mamaheux/bass-amplifier/cases/footswitch/plates/side_right.SLDPRT

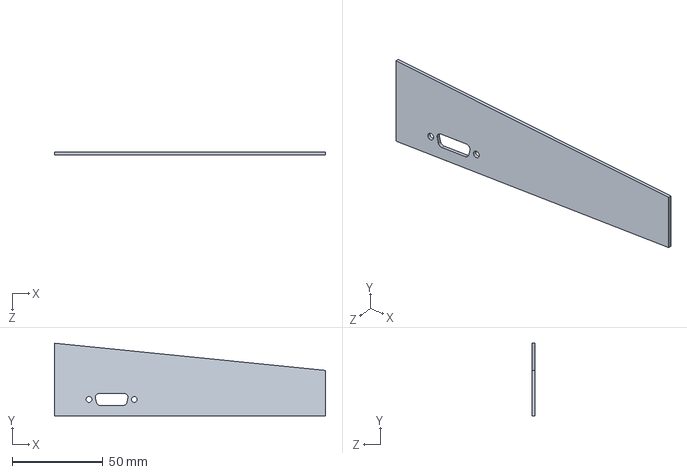
[picture p21: CAD file, 2020-08-28]
cases/footswitch/plates/side_right.SLDPRT
149.2 x 40.0 x 1.59 mm
