mamaheux/bass-amplifier/cases/amplifier/pieces/led_green.SLDPRT

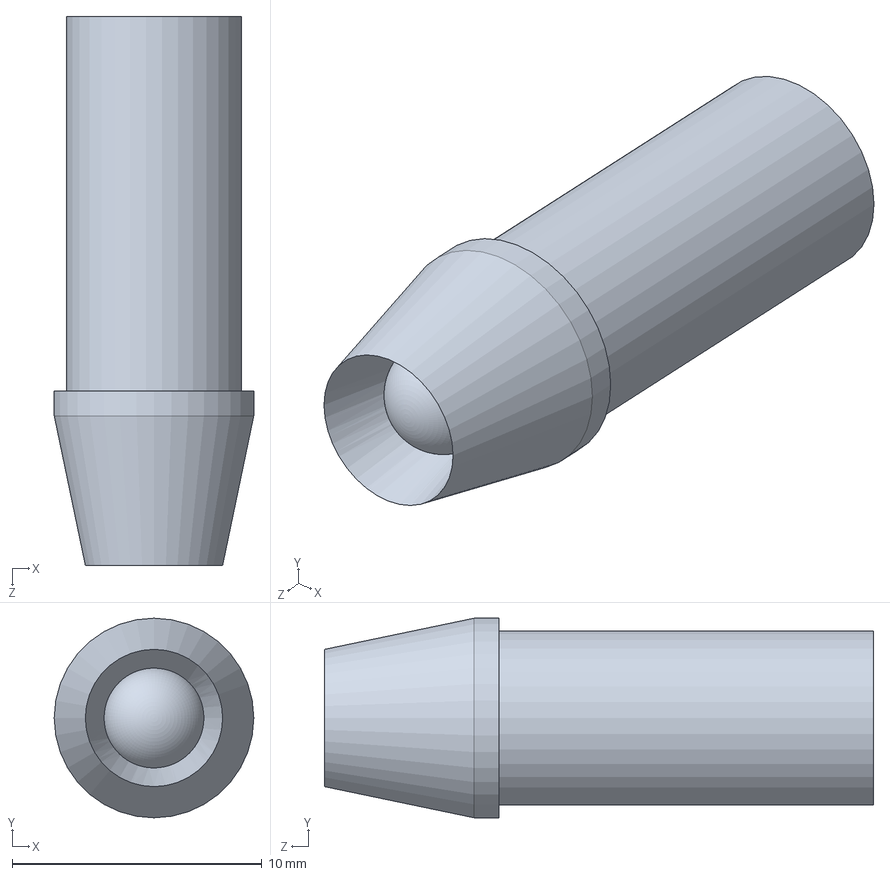
[picture p22: CAD file, 2020-08-28]
cases/amplifier/pieces/led_green.SLDPRT
8.00 x 8.00 x 22.0 mm
