mamaheux/bass-amplifier/cases/amplifier/plates/middle.SLDPRT

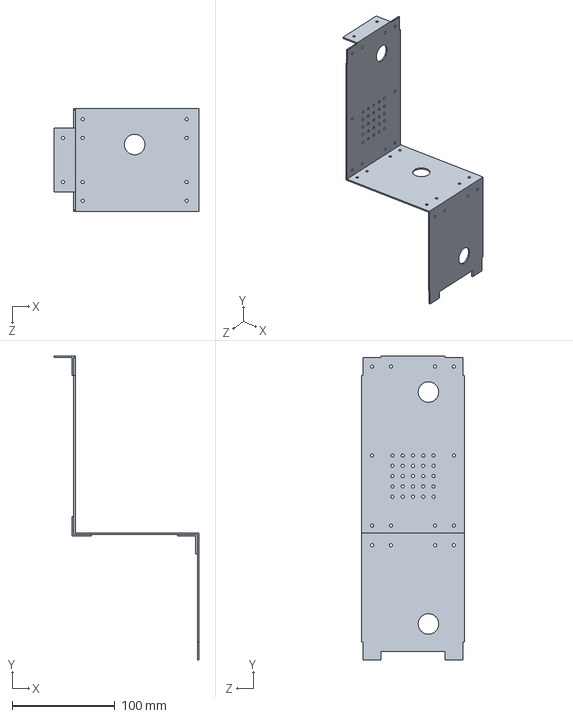
[picture p23: CAD file, 2020-08-28]
cases/amplifier/plates/middle.SLDPRT
140.6 x 295.2 x 100.0 mm
