mamaheux/bass-amplifier/cases/footswitch/pieces/led_red.SLDPRT

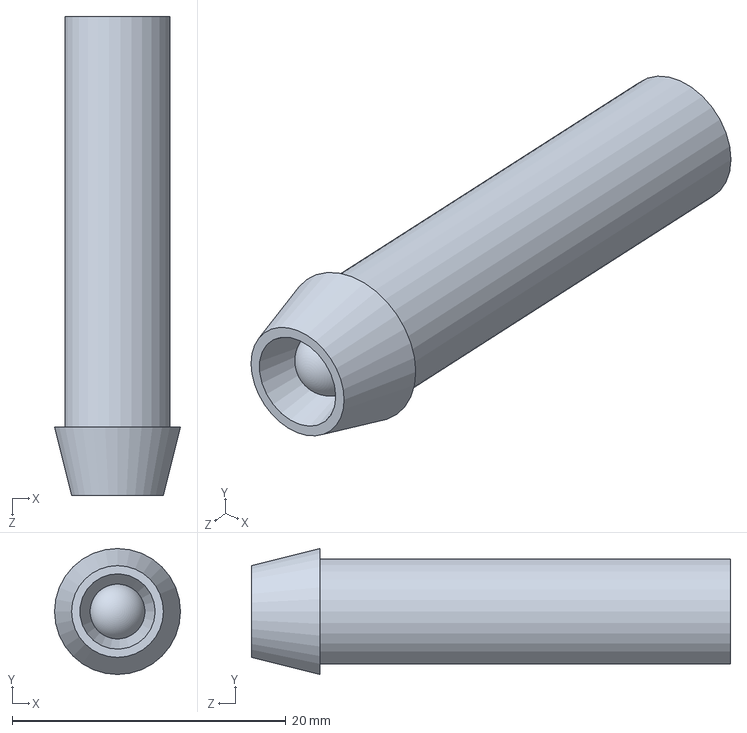
[picture p24: CAD file, 2020-08-28]
cases/footswitch/pieces/led_red.SLDPRT
9.20 x 9.20 x 35.0 mm
