mamaheux/bass-amplifier/cases/amplifier/pieces/transformer_600VA_50V.SLDPRT

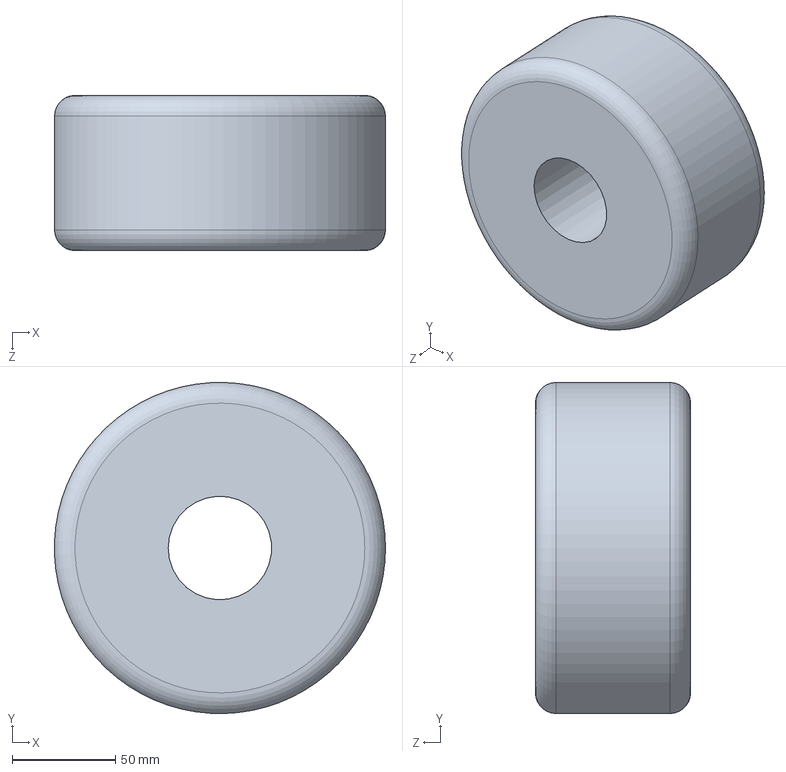
[picture p25: CAD file, 2020-08-28]
cases/amplifier/pieces/transformer_600VA_50V.SLDPRT
159.9 x 160.0 x 75.0 mm
