mamaheux/bass-amplifier/cases/footswitch/pieces/standoff_m3_10mm.SLDPRT

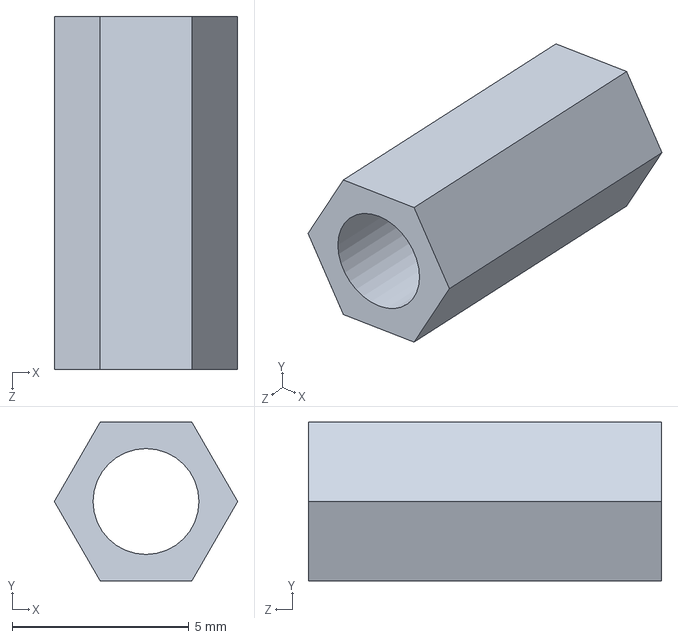
[picture p26: CAD file, 2020-08-28]
cases/footswitch/pieces/standoff_m3_10mm.SLDPRT
5.20 x 4.50 x 10.0 mm
