mamaheux/bass-amplifier/cases/amplifier/pieces/iec_c14.SLDPRT

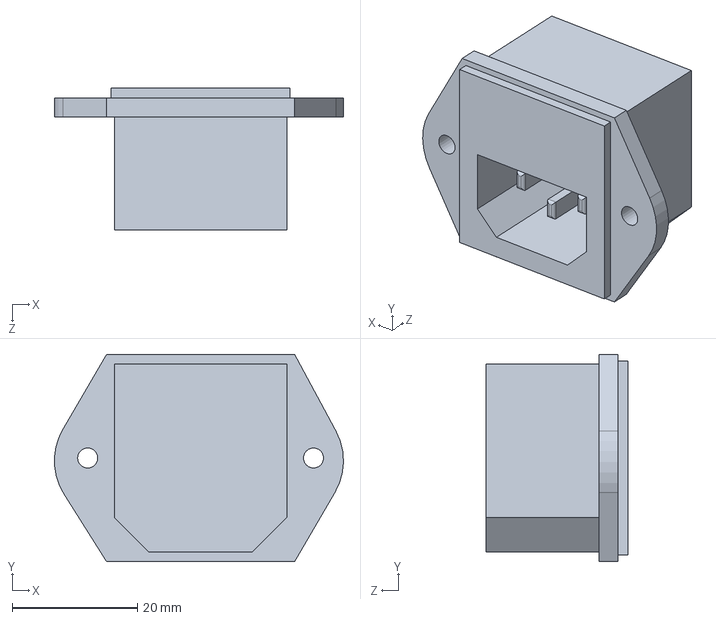
[picture p27: CAD file, 2020-08-28]
cases/amplifier/pieces/iec_c14.SLDPRT
46.1 x 33.0 x 22.6 mm
