mamaheux/bass-amplifier/cases/amplifier/plates/bottom.SLDPRT

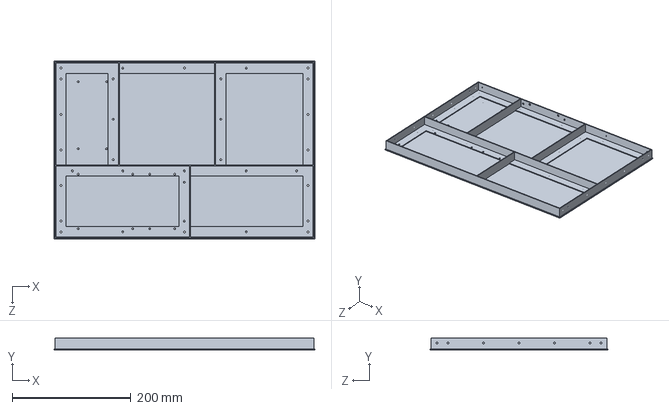
[picture p28: CAD file, 2020-08-28]
cases/amplifier/plates/bottom.SLDPRT
440.0 x 20.6 x 300.0 mm
