mamaheux/bass-amplifier/cases/amplifier/pieces/pcb_amp.SLDPRT

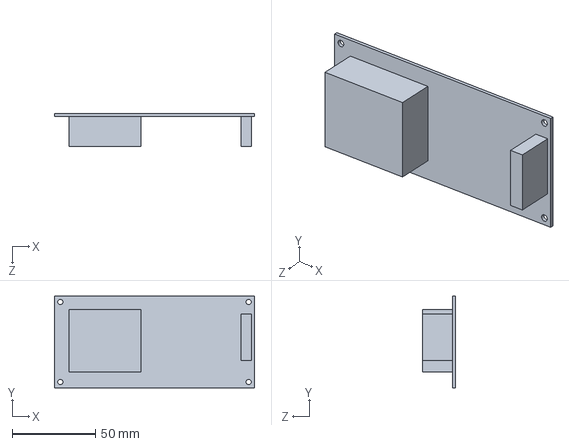
[picture p29: CAD file, 2020-08-28]
cases/amplifier/pieces/pcb_amp.SLDPRT
120.0 x 55.0 x 19.6 mm
