mamaheux/bass-amplifier/cases/amplifier/pieces/xlr.SLDPRT

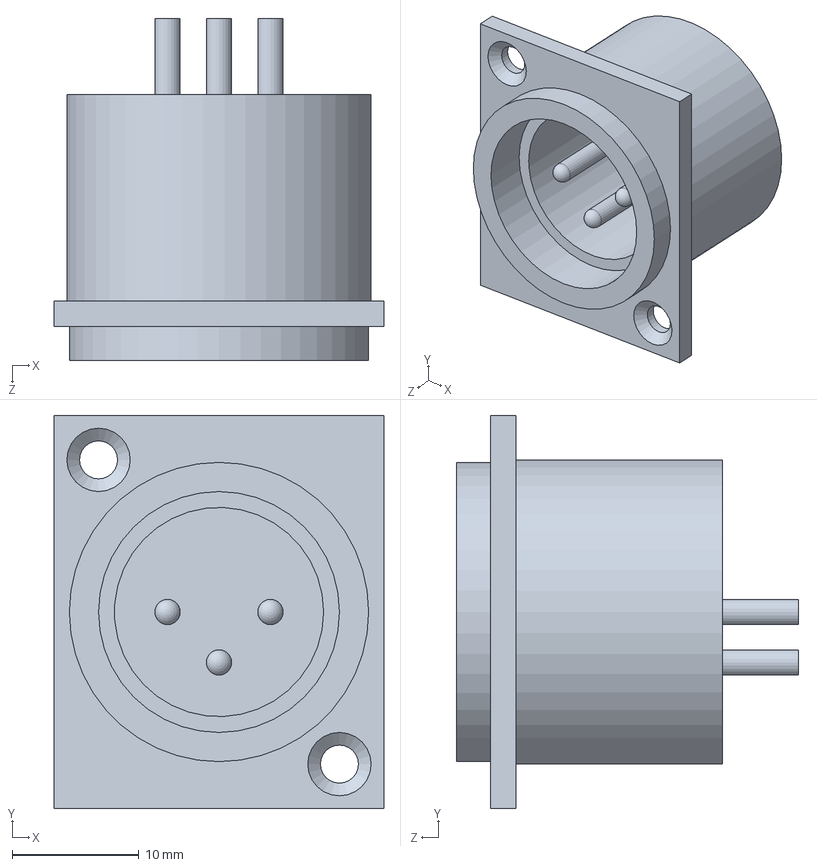
[picture p30: CAD file, 2020-08-28]
cases/amplifier/pieces/xlr.SLDPRT
26.0 x 31.0 x 27.0 mm
