mamaheux/bass-amplifier/cases/amplifier/pieces/fan_80mm.step.SLDPRT

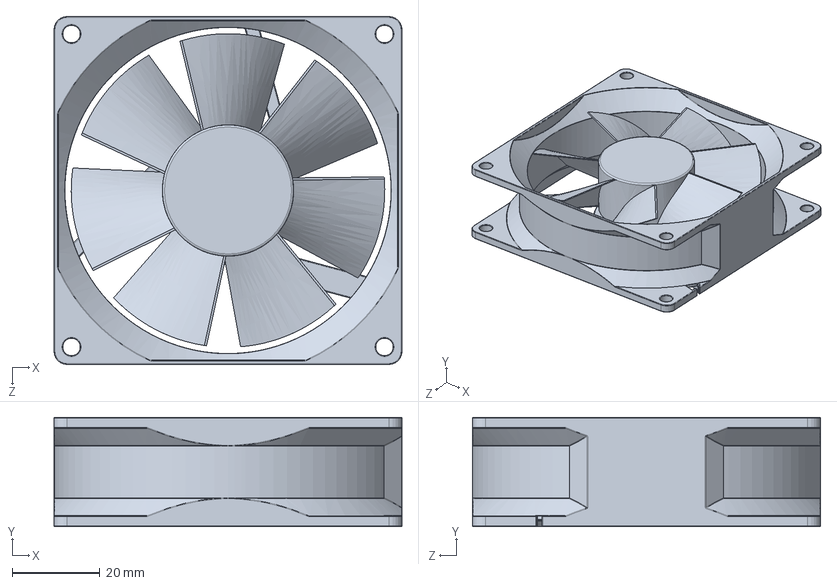
[picture p31: CAD file, 2020-08-28]
cases/amplifier/pieces/fan_80mm.step.SLDPRT
79.5 x 25.0 x 79.5 mm
