mamaheux/bass-amplifier/cases/amplifier/pieces/speakon.SLDPRT

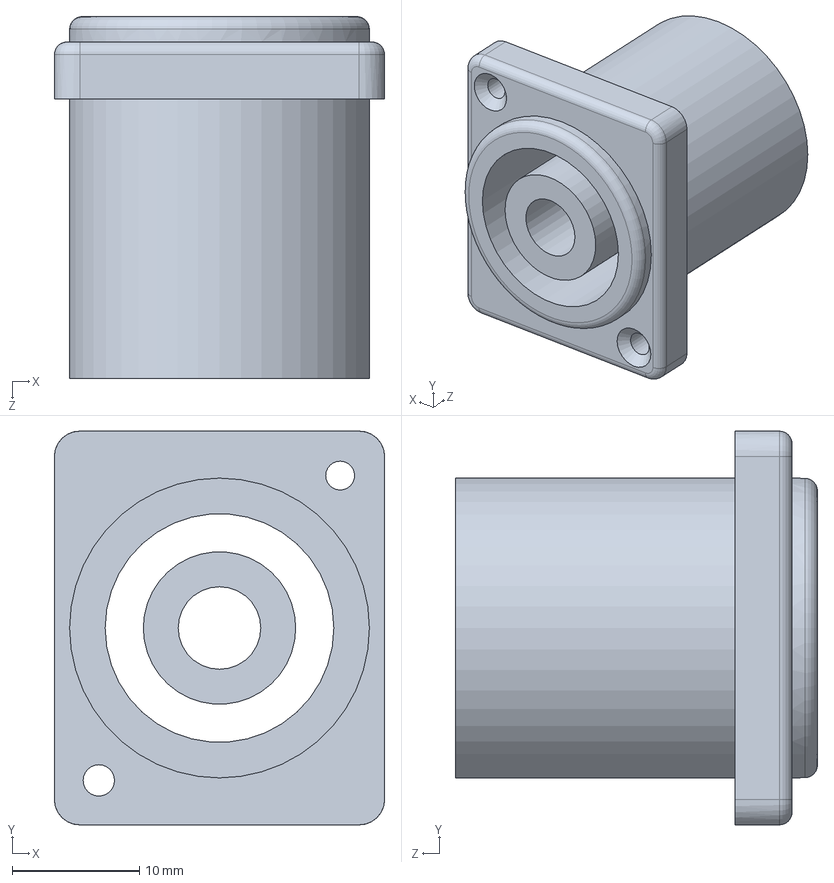
[picture p32: CAD file, 2020-08-28]
cases/amplifier/pieces/speakon.SLDPRT
26.0 x 31.0 x 28.5 mm
