mamaheux/bass-amplifier/cases/amplifier/pieces/button.SLDPRT

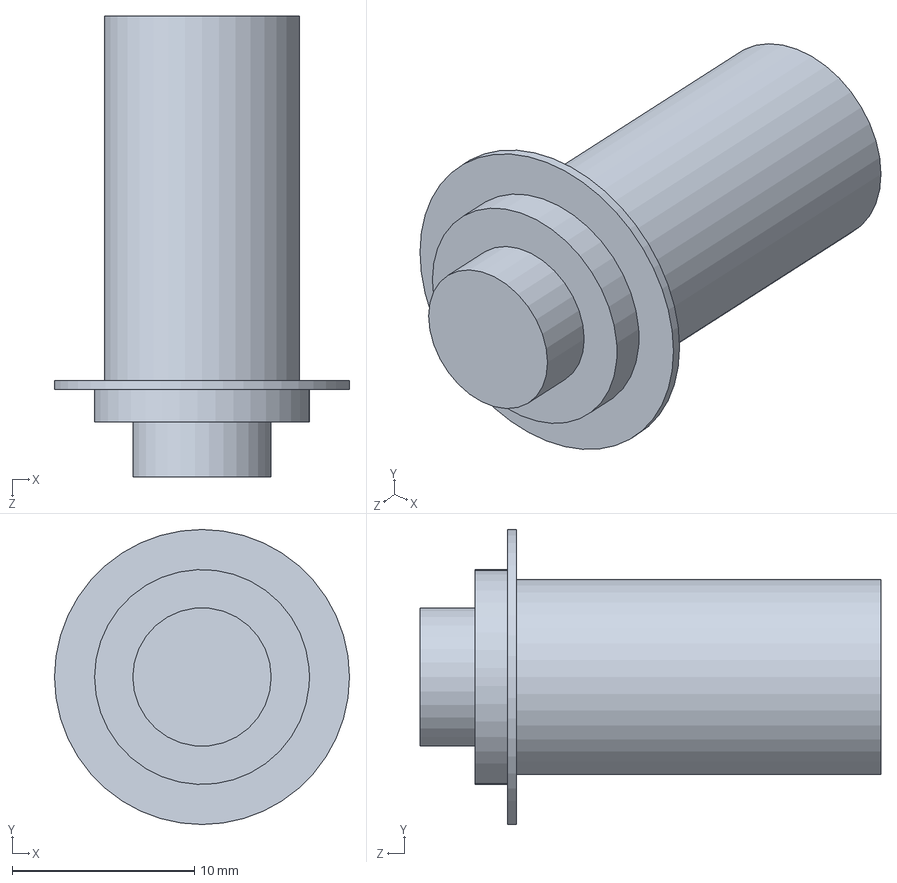
[picture p33: CAD file, 2020-08-28]
cases/amplifier/pieces/button.SLDPRT
16.2 x 16.2 x 25.3 mm
