mamaheux/bass-amplifier/cases/amplifier/pieces/knob.SLDPRT

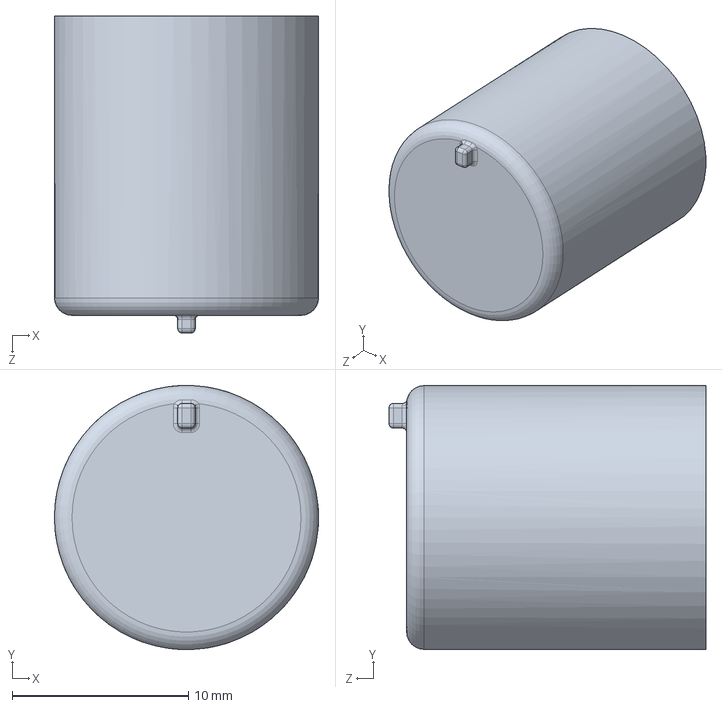
[picture p34: CAD file, 2020-08-28]
cases/amplifier/pieces/knob.SLDPRT
15.0 x 15.0 x 18.0 mm
