mamaheux/bass-amplifier/cases/amplifier/pieces/toggle_sw.SLDPRT

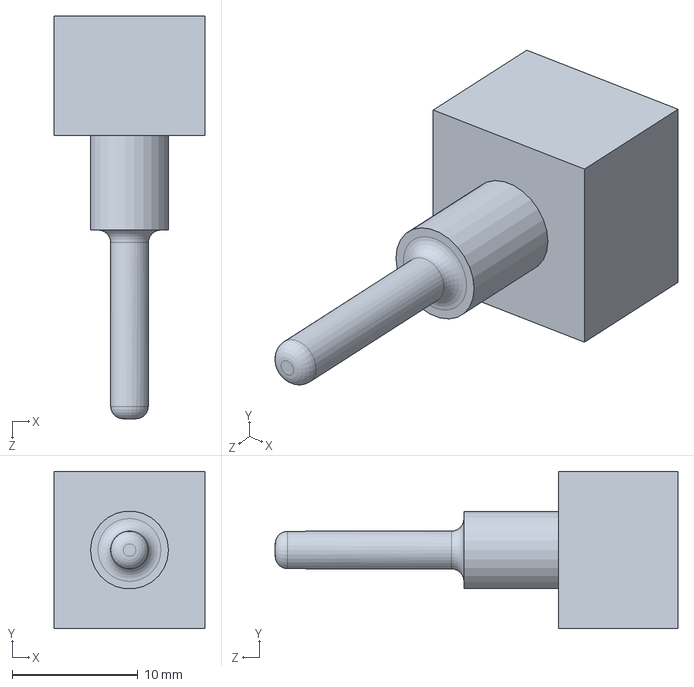
[picture p35: CAD file, 2020-08-28]
cases/amplifier/pieces/toggle_sw.SLDPRT
12.0 x 12.5 x 32.0 mm
