mamaheux/bass-amplifier/cases/amplifier/pieces/pcb_psu.SLDPRT

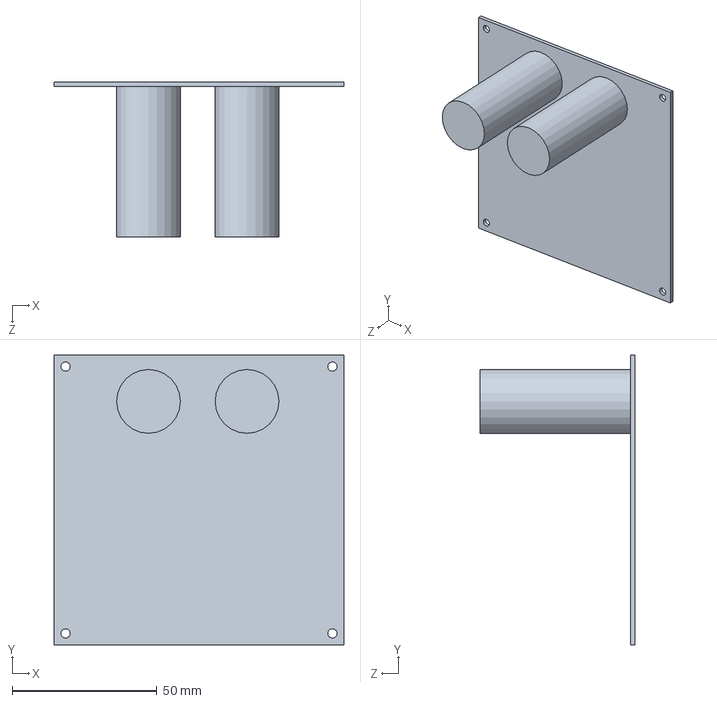
[picture p36: CAD file, 2020-08-28]
cases/amplifier/pieces/pcb_psu.SLDPRT
100.0 x 100.0 x 53.6 mm
