mamaheux/bass-amplifier/cases/amplifier/pieces/transformer_50VA_18V.SLDPRT

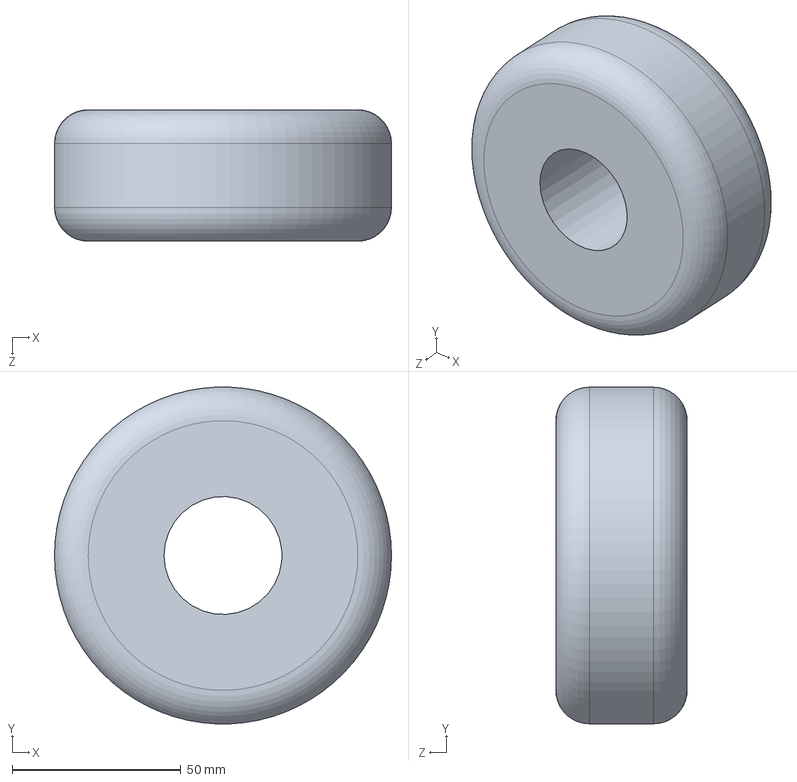
[picture p37: CAD file, 2020-08-28]
cases/amplifier/pieces/transformer_50VA_18V.SLDPRT
100.0 x 99.9 x 39.0 mm
