mamaheux/bass-amplifier/cases/amplifier/pieces/diode_bridge.SLDPRT

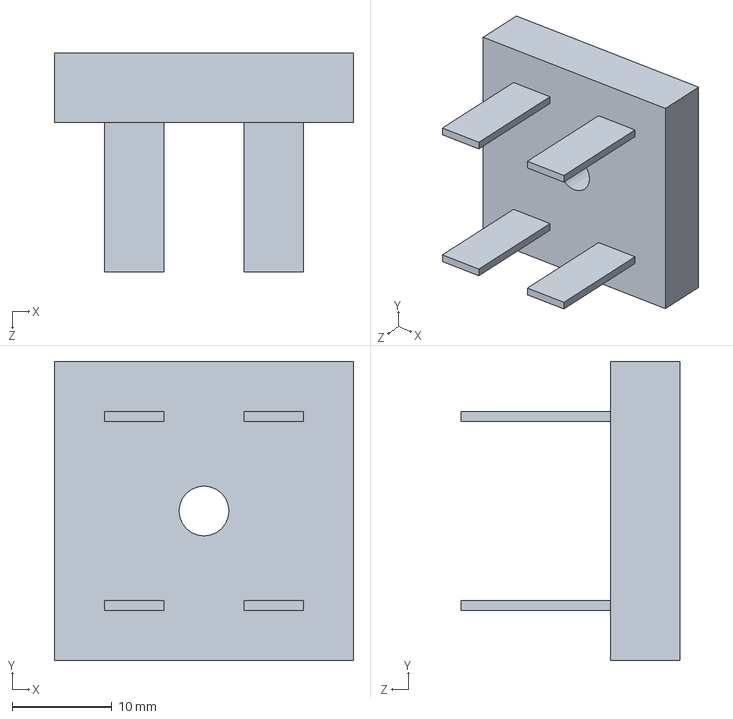
[picture p38: CAD file, 2020-08-28]
cases/amplifier/pieces/diode_bridge.SLDPRT
30.0 x 30.0 x 22.0 mm
