mamaheux/bass-amplifier/cases/amplifier/pieces/power_cap.SLDPRT

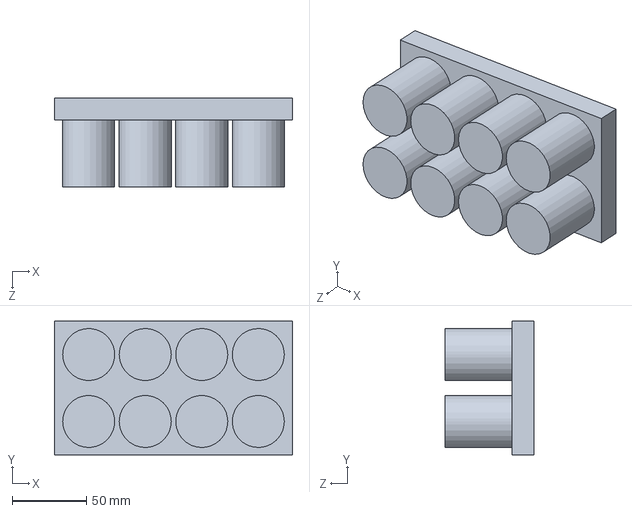
[picture p39: CAD file, 2020-08-28]
cases/amplifier/pieces/power_cap.SLDPRT
160.0 x 90.0 x 60.0 mm
