mamaheux/bass-amplifier/cases/amplifier/pieces/pot.SLDPRT

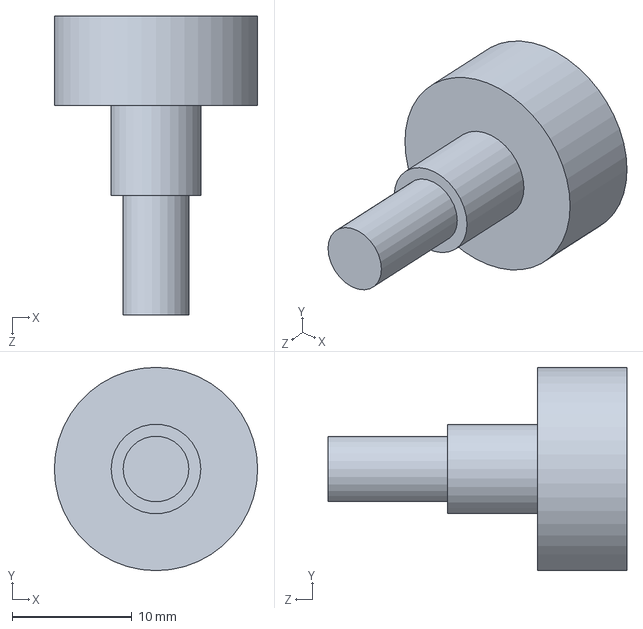
[picture p40: CAD file, 2020-08-28]
cases/amplifier/pieces/pot.SLDPRT
17.0 x 17.0 x 25.0 mm
