mamaheux/bass-amplifier/electronics/simulation/octaver_down.asc

A1: dflop
C1: cap; 10µ
C2: cap; 0.047µ
M1: nmos
M2: nmos
R1: res; 10k
R2: res; 10k
R3: res; 10k
R4: res; 10k
R5: res; 20k
R6: res; 20k
R7: res; 5.11k
R8: res; 5.11k
R9: res; 10k
R10: res; 5.11k
R11: res; 10k
R12: res; 20k
R13: res; 4.75k
R14: res; 10k
U1: LT1720
U2: LT1720
U3: AD824
U5: AD824
U6: AD824
U7: LT1720
U8: AD824
U9: AD824
V1: voltage; 1.65
V2: voltage; SINE(1.65 1 100); AC 1 0
V3: voltage; 1.65
Named nets: 0, v1.65, v3.3, signal, inv_signal, SW_signal, SW_inv_signal
.tran 0 0.5 0.3 startup
