mamaheux/bass-amplifier/code/processing/src/main_test.cpp

#include "config.h"

#include <Arduino.h>

#include <EffectProcessing.h>

#include <math.h>
#include <stdio.h>

#ifdef TEST

constexpr float MAX_ABS_ERROR = 0.00001;

#define TEST_ASSERT_FLOAT_WITHIN(t, e, v) if (abs(e - v) > t) \
    { \
        char buffer [50]; \
        sprintf(buffer, "%f", (double)e); \
        Serial.printf("Line %d | %s != ", __LINE__, buffer); \
        sprintf(buffer, "%f", (double)v); \
        Serial.printf("%s\n", buffer); \
    }

#define RUN_TEST(test) \
    do \
    { \
        Serial.printf("Running: %s \n", #test); \
        uint32_t start = micros(); \
        test(); \
        uint32_t duration = micros() - start; \
        Serial.printf("Elapsed time: %d us\n\n", duration); \
    } while(false);


constexpr uint32_t TEST_BLOCK_SIZE = 32;
constexpr uint32_t TEST_MAX_DELAY = 96;

Eq<TEST_BLOCK_SIZE> eq;
Presence<TEST_BLOCK_SIZE> presence;
Contour<TEST_BLOCK_SIZE> contour;
Compressor<TEST_BLOCK_SIZE> compressor;
Octaver<TEST_BLOCK_SIZE> octaver;
DMAMEM Delay<TEST_BLOCK_SIZE, TEST_MAX_DELAY> delayEffect;
Reverb<TEST_BLOCK_SIZE> reverb;
Overdrive<TEST_BLOCK_SIZE> overdrive;
Mute<TEST_BLOCK_SIZE> mute;

void test_biquad()
{
    constexpr uint32_t NUM_STAGES = 1;
    const float COEFFICIENTS[] = {0.00554272, 0.01108543, 0.00554272, 1.77863178, -0.80080265};
    float input[TEST_BLOCK_SIZE] = {1, 0, 0, 0, 0, 0, 0, 0};

    BiquadIir<TEST_BLOCK_SIZE, NUM_STAGES> biquadIir;
    biquadIir.update(COEFFICIENTS);

    float* output = biquadIir.process(input);

    TEST_ASSERT_FLOAT_WITHIN(MAX_ABS_ERROR, 0.00554272, output[0]);
    TEST_ASSERT_FLOAT_WITHIN(MAX_ABS_ERROR, 0.02094389, output[1]);
    TEST_ASSERT_FLOAT_WITHIN(MAX_ABS_ERROR, 0.03835556, output[2]);
    TEST_ASSERT_FLOAT_WITHIN(MAX_ABS_ERROR, 0.05144849, output[3]);
    TEST_ASSERT_FLOAT_WITHIN(MAX_ABS_ERROR, 0.06079269, output[4]);
    TEST_ASSERT_FLOAT_WITHIN(MAX_ABS_ERROR, 0.06692773, output[5]);
    TEST_ASSERT_FLOAT_WITHIN(MAX_ABS_ERROR, 0.07035683, output[6]);
    TEST_ASSERT_FLOAT_WITHIN(MAX_ABS_ERROR, 0.071543, output[7]);
}

void test_feedbackComb()
{
    constexpr uint32_t DELAY = 2;
    const float GAIN = 0.9;
    float input[2 * TEST_BLOCK_SIZE] = {0.1, 0.2, 0.3, 0.4, 0.3, 0.2, 0.1, 0};

    FeedbackComb<TEST_BLOCK_SIZE, DELAY> feedbackComb;
    feedbackComb.update(GAIN);

    float* output = feedbackComb.process(input);
    TEST_ASSERT_FLOAT_WITHIN(MAX_ABS_ERROR, 0, output[0]);
    TEST_ASSERT_FLOAT_WITHIN(MAX_ABS_ERROR, 0, output[1]);
    TEST_ASSERT_FLOAT_WITHIN(MAX_ABS_ERROR, 0.1, output[2]);
    TEST_ASSERT_FLOAT_WITHIN(MAX_ABS_ERROR, 0.2, output[3]);
    TEST_ASSERT_FLOAT_WITHIN(MAX_ABS_ERROR, 0.39, output[4]);
    TEST_ASSERT_FLOAT_WITHIN(MAX_ABS_ERROR, 0.58, output[5]);
    TEST_ASSERT_FLOAT_WITHIN(MAX_ABS_ERROR, 0.651, output[6]);
    TEST_ASSERT_FLOAT_WITHIN(MAX_ABS_ERROR, 0.722, output[7]);

    output = feedbackComb.process(input + TEST_BLOCK_SIZE);
    TEST_ASSERT_FLOAT_WITHIN(MAX_ABS_ERROR, 0.19371842, output[0]);
    TEST_ASSERT_FLOAT_WITHIN(MAX_ABS_ERROR, 0.18352271, output[1]);
    TEST_ASSERT_FLOAT_WITHIN(MAX_ABS_ERROR, 0.17434658, output[2]);
    TEST_ASSERT_FLOAT_WITHIN(MAX_ABS_ERROR, 0.16517044, output[3]);
    TEST_ASSERT_FLOAT_WITHIN(MAX_ABS_ERROR, 0.15691192, output[4]);
    TEST_ASSERT_FLOAT_WITHIN(MAX_ABS_ERROR, 0.1486534, output[5]);
    TEST_ASSERT_FLOAT_WITHIN(MAX_ABS_ERROR, 0.14122073, output[6]);
    TEST_ASSERT_FLOAT_WITHIN(MAX_ABS_ERROR, 0.13378806, output[7]);
}

void test_allPassComb()
{
    constexpr uint32_t DELAY = 2;
    const float GAIN = 0.9;
    float input[2 * TEST_BLOCK_SIZE] = {10, 20, 30, 40, 30, 20, 10, 0};

    AllPassComb<TEST_BLOCK_SIZE, DELAY> allPassComb;
    allPassComb.update(GAIN);

    float* output = allPassComb.process(input);
    TEST_ASSERT_FLOAT_WITHIN(MAX_ABS_ERROR, 9.007179, output[0]);
    TEST_ASSERT_FLOAT_WITHIN(MAX_ABS_ERROR, 18.006821, output[1]);
    TEST_ASSERT_FLOAT_WITHIN(MAX_ABS_ERROR, 28.893539, output[2]);
    TEST_ASSERT_FLOAT_WITHIN(MAX_ABS_ERROR, 39.793861, output[3]);
    TEST_ASSERT_FLOAT_WITHIN(MAX_ABS_ERROR, 30.995815, output[4]);
    TEST_ASSERT_FLOAT_WITHIN(MAX_ABS_ERROR, 22.185524, output[5]);
    TEST_ASSERT_FLOAT_WITHIN(MAX_ABS_ERROR, 11.103766, output[6]);
    TEST_ASSERT_FLOAT_WITHIN(MAX_ABS_ERROR, 0.033028, output[7]);

    output = allPassComb.process(input + TEST_BLOCK_SIZE);
    TEST_ASSERT_FLOAT_WITHIN(MAX_ABS_ERROR, 0.001867, output[0]);
    TEST_ASSERT_FLOAT_WITHIN(MAX_ABS_ERROR, -0.008395, output[1]);
    TEST_ASSERT_FLOAT_WITHIN(MAX_ABS_ERROR, -0.001680, output[2]);
    TEST_ASSERT_FLOAT_WITHIN(MAX_ABS_ERROR, 0.007556, output[3]);
    TEST_ASSERT_FLOAT_WITHIN(MAX_ABS_ERROR, 0.001512, output[4]);
    TEST_ASSERT_FLOAT_WITHIN(MAX_ABS_ERROR, -0.006800, output[5]);
    TEST_ASSERT_FLOAT_WITHIN(MAX_ABS_ERROR, -0.001361, output[6]);
    TEST_ASSERT_FLOAT_WITHIN(MAX_ABS_ERROR, 0.006120, output[7]);
}

void test_contour()
{
    const float COEFFICIENTS[] = {2, 0, 0, 0, 0, 0.5, 0, 0, 0, 0, 0.5};
    float input[TEST_BLOCK_SIZE] = {1, 0, 0, 0, 0, 0, 0, 0};

    contour.update(reinterpret_cast<const uint8_t*>(COEFFICIENTS));

    float* output = contour.process(input);

    TEST_ASSERT_FLOAT_WITHIN(MAX_ABS_ERROR, 0.5, output[0]);
    TEST_ASSERT_FLOAT_WITHIN(MAX_ABS_ERROR, 0, output[1]);
    TEST_ASSERT_FLOAT_WITHIN(MAX_ABS_ERROR, 0, output[2]);
    TEST_ASSERT_FLOAT_WITHIN(MAX_ABS_ERROR, 0, output[3]);
    TEST_ASSERT_FLOAT_WITHIN(MAX_ABS_ERROR, 0, output[4]);
    TEST_ASSERT_FLOAT_WITHIN(MAX_ABS_ERROR, 0, output[5]);
    TEST_ASSERT_FLOAT_WITHIN(MAX_ABS_ERROR, 0, output[6]);
    TEST_ASSERT_FLOAT_WITHIN(MAX_ABS_ERROR, 0, output[7]);
}

void test_presence()
{
    const float COEFFICIENTS[] = {2, 0, 0, 0, 0, 0.5};
    float input[TEST_BLOCK_SIZE] = {1, 0, 0, 0, 0, 0, 0, 0};

    presence.update(reinterpret_cast<const uint8_t*>(COEFFICIENTS));

    float* output = presence.process(input);

    TEST_ASSERT_FLOAT_WITHIN(MAX_ABS_ERROR, 2, output[0]);
    TEST_ASSERT_FLOAT_WITHIN(MAX_ABS_ERROR, 0, output[1]);
    TEST_ASSERT_FLOAT_WITHIN(MAX_ABS_ERROR, 0, output[2]);
    TEST_ASSERT_FLOAT_WITHIN(MAX_ABS_ERROR, 0, output[3]);
    TEST_ASSERT_FLOAT_WITHIN(MAX_ABS_ERROR, 0, output[4]);
    TEST_ASSERT_FLOAT_WITHIN(MAX_ABS_ERROR, 0, output[5]);
    TEST_ASSERT_FLOAT_WITHIN(MAX_ABS_ERROR, 0, output[6]);
    TEST_ASSERT_FLOAT_WITHIN(MAX_ABS_ERROR, 0, output[7]);
}

void test_eq()
{
    const float COEFFICIENTS[] = {2, 0, 0, 0, 0, 0.5, 0, 0, 0, 0, 0.25, 0, 0, 0, 0, 4, 0, 0, 0, 0, 8, 0, 0, 0, 0, 0.125, 0, 0, 0, 0, 5, 0, 0, 0, 0, 0.2, 0, 0, 0, 0};
    float input[TEST_BLOCK_SIZE] = {1, 0, 0, 0, 0, 0, 0, 0};

    eq.update(reinterpret_cast<const uint8_t*>(COEFFICIENTS));

    float* output = eq.process(input);

    TEST_ASSERT_FLOAT_WITHIN(MAX_ABS_ERROR, 1, output[0]);
    TEST_ASSERT_FLOAT_WITHIN(MAX_ABS_ERROR, 0, output[1]);
    TEST_ASSERT_FLOAT_WITHIN(MAX_ABS_ERROR, 0, output[2]);
    TEST_ASSERT_FLOAT_WITHIN(MAX_ABS_ERROR, 0, output[3]);
    TEST_ASSERT_FLOAT_WITHIN(MAX_ABS_ERROR, 0, output[4]);
    TEST_ASSERT_FLOAT_WITHIN(MAX_ABS_ERROR, 0, output[5]);
    TEST_ASSERT_FLOAT_WITHIN(MAX_ABS_ERROR, 0, output[6]);
    TEST_ASSERT_FLOAT_WITHIN(MAX_ABS_ERROR, 0, output[7]);
}

void test_compressor()
{
    const float COEFFICIENTS[] = {0.15, 0.5, 0.5, 0.75};
    float input[TEST_BLOCK_SIZE] = {0.1, 0.2, 0.3, 0.4, 0.3, 0.2, 0.1, 0};

    compressor.update(reinterpret_cast<const uint8_t*>(COEFFICIENTS));

    float* output = compressor.process(input);

    TEST_ASSERT_FLOAT_WITHIN(MAX_ABS_ERROR, 0.1, output[0]);
    TEST_ASSERT_FLOAT_WITHIN(MAX_ABS_ERROR, 0.2, output[1]);
    TEST_ASSERT_FLOAT_WITHIN(MAX_ABS_ERROR, 0.25588235, output[2]);
    TEST_ASSERT_FLOAT_WITHIN(MAX_ABS_ERROR, 0.29795918, output[3]);
    TEST_ASSERT_FLOAT_WITHIN(MAX_ABS_ERROR, 0.22384615, output[4]);
    TEST_ASSERT_FLOAT_WITHIN(MAX_ABS_ERROR, 0.15385694, output[5]);
    TEST_ASSERT_FLOAT_WITHIN(MAX_ABS_ERROR, 0.08206681, output[6]);
    TEST_ASSERT_FLOAT_WITHIN(MAX_ABS_ERROR, 0, output[7]);
}

void test_octaver()
{
    const float COEFFICIENTS[] = {2, 0, 0, 0, 0, 4, 0, 0, 0, 0, 0.5, 0, 0, 0, 0, 0.25, 0.75};
    float input[TEST_BLOCK_SIZE] = {1, 2, -1, -2};

    octaver.update(reinterpret_cast<const uint8_t*>(COEFFICIENTS));

    float* output = octaver.process(input);

    TEST_ASSERT_FLOAT_WITHIN(MAX_ABS_ERROR, 1.0, output[0]);
    TEST_ASSERT_FLOAT_WITHIN(MAX_ABS_ERROR, 2.0, output[1]);
    TEST_ASSERT_FLOAT_WITHIN(MAX_ABS_ERROR, 0.5, output[2]);
    TEST_ASSERT_FLOAT_WITHIN(MAX_ABS_ERROR, 1.0, output[3]);
}

void test_delay()
{
    uint8_t data[8];
    float volume = 0.95;
    uint32_t delayValue = 1;
    memcpy(data, &volume, sizeof(float));
    memcpy(data + sizeof(float), &delayValue, sizeof(uint32_t));

    float input[TEST_BLOCK_SIZE] = {1, 0, 0, 0};

    delayEffect.update(data);

    float* output = delayEffect.process(input);
    TEST_ASSERT_FLOAT_WITHIN(MAX_ABS_ERROR, 1, output[0]);
    TEST_ASSERT_FLOAT_WITHIN(MAX_ABS_ERROR, 0.95, output[1]);
    TEST_ASSERT_FLOAT_WITHIN(MAX_ABS_ERROR, 0.9025, output[2]);
    TEST_ASSERT_FLOAT_WITHIN(MAX_ABS_ERROR, 0.857375, output[3]);

    input[0] = 0;
    output = delayEffect.process(input);
    TEST_ASSERT_FLOAT_WITHIN(MAX_ABS_ERROR, 0.19371148, output[0]);

    output = delayEffect.process(input);
    TEST_ASSERT_FLOAT_WITHIN(MAX_ABS_ERROR, 0.0375241392, output[0]);

    output = delayEffect.process(input);
    TEST_ASSERT_FLOAT_WITHIN(MAX_ABS_ERROR, 0.0072688567, output[0]);
    TEST_ASSERT_FLOAT_WITHIN(MAX_ABS_ERROR, 0.0069054139, output[1]);
}

void test_reverb()
{
    float volume = 0.95;

    float input[TEST_BLOCK_SIZE] = {1, 0, 0, 0};

    reverb.update(reinterpret_cast<uint8_t*>(&volume));

    float* output = reverb.process(input);
    TEST_ASSERT_FLOAT_WITHIN(MAX_ABS_ERROR, 0.5, output[0]);
}

void test_overdrive()
{
    const float COEFFICIENTS[] = {4, 2, 0, 0, 0, 0};
    float input[TEST_BLOCK_SIZE] = {0.1, 0.2, 0.3, 0.4, 0.3, 0.2, 0.1};

    overdrive.update(reinterpret_cast<const uint8_t*>(COEFFICIENTS));

    float* output = overdrive.process(input);

    TEST_ASSERT_FLOAT_WITHIN(MAX_ABS_ERROR, 0.59020401, output[0]);
    TEST_ASSERT_FLOAT_WITHIN(MAX_ABS_ERROR, 0.94818084, output[1]);
    TEST_ASSERT_FLOAT_WITHIN(MAX_ABS_ERROR, 1.16530476, output[2]);
    TEST_ASSERT_FLOAT_WITHIN(MAX_ABS_ERROR, 1.29699708, output[3]);
    TEST_ASSERT_FLOAT_WITHIN(MAX_ABS_ERROR, 1.16530476, output[4]);
    TEST_ASSERT_FLOAT_WITHIN(MAX_ABS_ERROR, 0.94818084, output[5]);
    TEST_ASSERT_FLOAT_WITHIN(MAX_ABS_ERROR, 0.59020401, output[6]);
}

void test_mute()
{
    float input[TEST_BLOCK_SIZE] = {0.1, 0.2, 0.3, 0.4, 0.3, 0.2, 0.1};

    float* output = mute.process(input);

    TEST_ASSERT_FLOAT_WITHIN(MAX_ABS_ERROR, 0, output[0]);
    TEST_ASSERT_FLOAT_WITHIN(MAX_ABS_ERROR, 0, output[1]);
    TEST_ASSERT_FLOAT_WITHIN(MAX_ABS_ERROR, 0, output[2]);
    TEST_ASSERT_FLOAT_WITHIN(MAX_ABS_ERROR, 0, output[3]);
    TEST_ASSERT_FLOAT_WITHIN(MAX_ABS_ERROR, 0, output[4]);
    TEST_ASSERT_FLOAT_WITHIN(MAX_ABS_ERROR, 0, output[5]);
    TEST_ASSERT_FLOAT_WITHIN(MAX_ABS_ERROR, 0, output[6]);
}

void randomize(float* input, uint32_t blockSize)
{
    for (uint32_t i = 0; i < blockSize; i++)
    {
        input[i] = (static_cast<float>(rand()) / static_cast<float>(RAND_MAX)) - 0.5;
    }
}

void test_performance()
{
    constexpr uint32_t ITERATION_COUNT = 1500;
    float input[TEST_BLOCK_SIZE];

    uint32_t durationTotal = 0;

    for (uint32_t i = 0; i < ITERATION_COUNT; i++)
    {
        randomize(input, TEST_BLOCK_SIZE);

        uint32_t start = micros();
        float* output = contour.process(input);
        output = presence.process(output);
        output = eq.process(output);

        output = compressor.process(output);
        output = octaver.process(output);
        output = delayEffect.process(output);
        output = reverb.process(output);
        output = overdrive.process(output);
        durationTotal += micros() - start;
    }

    Serial.printf("Duration = %d us\n", durationTotal / ITERATION_COUNT);
}

void test_isEnabled_contour()
{
    float input[TEST_BLOCK_SIZE] = {0.1, 0.2, 0.3, 0.4, 0.3, 0.2, 0.1};

    contour.setIsEnabled(false);
    float* output = contour.process(input);

    TEST_ASSERT_FLOAT_WITHIN(MAX_ABS_ERROR, 0.1, output[0]);
    TEST_ASSERT_FLOAT_WITHIN(MAX_ABS_ERROR, 0.2, output[1]);
    TEST_ASSERT_FLOAT_WITHIN(MAX_ABS_ERROR, 0.3, output[2]);
    TEST_ASSERT_FLOAT_WITHIN(MAX_ABS_ERROR, 0.4, output[3]);
    TEST_ASSERT_FLOAT_WITHIN(MAX_ABS_ERROR, 0.3, output[4]);
    TEST_ASSERT_FLOAT_WITHIN(MAX_ABS_ERROR, 0.2, output[5]);
    TEST_ASSERT_FLOAT_WITHIN(MAX_ABS_ERROR, 0.1, output[6]);
}

void test_isEnabled_presence()
{
    float input[TEST_BLOCK_SIZE] = {0.1, 0.2, 0.3, 0.4, 0.3, 0.2, 0.1};

    presence.setIsEnabled(false);
    float* output = presence.process(input);

    TEST_ASSERT_FLOAT_WITHIN(MAX_ABS_ERROR, 0.1, output[0]);
    TEST_ASSERT_FLOAT_WITHIN(MAX_ABS_ERROR, 0.2, output[1]);
    TEST_ASSERT_FLOAT_WITHIN(MAX_ABS_ERROR, 0.3, output[2]);
    TEST_ASSERT_FLOAT_WITHIN(MAX_ABS_ERROR, 0.4, output[3]);
    TEST_ASSERT_FLOAT_WITHIN(MAX_ABS_ERROR, 0.3, output[4]);
    TEST_ASSERT_FLOAT_WITHIN(MAX_ABS_ERROR, 0.2, output[5]);
    TEST_ASSERT_FLOAT_WITHIN(MAX_ABS_ERROR, 0.1, output[6]);
}

void test_isEnabled_eq()
{
    float input[TEST_BLOCK_SIZE] = {0.1, 0.2, 0.3, 0.4, 0.3, 0.2, 0.1};

    eq.setIsEnabled(false);
    float* output = eq.process(input);

    TEST_ASSERT_FLOAT_WITHIN(MAX_ABS_ERROR, 0.1, output[0]);
    TEST_ASSERT_FLOAT_WITHIN(MAX_ABS_ERROR, 0.2, output[1]);
    TEST_ASSERT_FLOAT_WITHIN(MAX_ABS_ERROR, 0.3, output[2]);
    TEST_ASSERT_FLOAT_WITHIN(MAX_ABS_ERROR, 0.4, output[3]);
    TEST_ASSERT_FLOAT_WITHIN(MAX_ABS_ERROR, 0.3, output[4]);
    TEST_ASSERT_FLOAT_WITHIN(MAX_ABS_ERROR, 0.2, output[5]);
    TEST_ASSERT_FLOAT_WITHIN(MAX_ABS_ERROR, 0.1, output[6]);
}

void test_isEnabled_compressor()
{
    float input[TEST_BLOCK_SIZE] = {0.1, 0.2, 0.3, 0.4, 0.3, 0.2, 0.1};

    compressor.setIsEnabled(false);
    float* output = compressor.process(input);

    TEST_ASSERT_FLOAT_WITHIN(MAX_ABS_ERROR, 0.1, output[0]);
    TEST_ASSERT_FLOAT_WITHIN(MAX_ABS_ERROR, 0.2, output[1]);
    TEST_ASSERT_FLOAT_WITHIN(MAX_ABS_ERROR, 0.3, output[2]);
    TEST_ASSERT_FLOAT_WITHIN(MAX_ABS_ERROR, 0.4, output[3]);
    TEST_ASSERT_FLOAT_WITHIN(MAX_ABS_ERROR, 0.3, output[4]);
    TEST_ASSERT_FLOAT_WITHIN(MAX_ABS_ERROR, 0.2, output[5]);
    TEST_ASSERT_FLOAT_WITHIN(MAX_ABS_ERROR, 0.1, output[6]);
}

void test_isEnabled_octaver()
{
    float input[TEST_BLOCK_SIZE] = {0.1, 0.2, 0.3, 0.4, 0.3, 0.2, 0.1};

    octaver.setIsEnabled(false);
    float* output = octaver.process(input);

    TEST_ASSERT_FLOAT_WITHIN(MAX_ABS_ERROR, 0.1, output[0]);
    TEST_ASSERT_FLOAT_WITHIN(MAX_ABS_ERROR, 0.2, output[1]);
    TEST_ASSERT_FLOAT_WITHIN(MAX_ABS_ERROR, 0.3, output[2]);
    TEST_ASSERT_FLOAT_WITHIN(MAX_ABS_ERROR, 0.4, output[3]);
    TEST_ASSERT_FLOAT_WITHIN(MAX_ABS_ERROR, 0.3, output[4]);
    TEST_ASSERT_FLOAT_WITHIN(MAX_ABS_ERROR, 0.2, output[5]);
    TEST_ASSERT_FLOAT_WITHIN(MAX_ABS_ERROR, 0.1, output[6]);
}

void test_isEnabled_delay()
{
    float input[TEST_BLOCK_SIZE] = {0.1, 0.2, 0.3, 0.4, 0.3, 0.2, 0.1};

    delayEffect.setIsEnabled(false);
    float* output = delayEffect.process(input);

    TEST_ASSERT_FLOAT_WITHIN(MAX_ABS_ERROR, 0.1, output[0]);
    TEST_ASSERT_FLOAT_WITHIN(MAX_ABS_ERROR, 0.2, output[1]);
    TEST_ASSERT_FLOAT_WITHIN(MAX_ABS_ERROR, 0.3, output[2]);
    TEST_ASSERT_FLOAT_WITHIN(MAX_ABS_ERROR, 0.4, output[3]);
    TEST_ASSERT_FLOAT_WITHIN(MAX_ABS_ERROR, 0.3, output[4]);
    TEST_ASSERT_FLOAT_WITHIN(MAX_ABS_ERROR, 0.2, output[5]);
    TEST_ASSERT_FLOAT_WITHIN(MAX_ABS_ERROR, 0.1, output[6]);
}

void test_isEnabled_reverb()
{
    float input[TEST_BLOCK_SIZE] = {0.1, 0.2, 0.3, 0.4, 0.3, 0.2, 0.1};

    reverb.setIsEnabled(false);
    float* output = reverb.process(input);

    TEST_ASSERT_FLOAT_WITHIN(MAX_ABS_ERROR, 0.05, output[0]);
    TEST_ASSERT_FLOAT_WITHIN(MAX_ABS_ERROR, 0.1, output[1]);
    TEST_ASSERT_FLOAT_WITHIN(MAX_ABS_ERROR, 0.15, output[2]);
    TEST_ASSERT_FLOAT_WITHIN(MAX_ABS_ERROR, 0.2, output[3]);
    TEST_ASSERT_FLOAT_WITHIN(MAX_ABS_ERROR, 0.15, output[4]);
    TEST_ASSERT_FLOAT_WITHIN(MAX_ABS_ERROR, 0.1, output[5]);
    TEST_ASSERT_FLOAT_WITHIN(MAX_ABS_ERROR, 0.05, output[6]);
}

void test_isEnabled_overdrive()
{
    float input[TEST_BLOCK_SIZE] = {0.1, 0.2, 0.3, 0.4, 0.3, 0.2, 0.1};

    overdrive.setIsEnabled(false);
    float* output = overdrive.process(input);

    TEST_ASSERT_FLOAT_WITHIN(MAX_ABS_ERROR, 0.1, output[0]);
    TEST_ASSERT_FLOAT_WITHIN(MAX_ABS_ERROR, 0.2, output[1]);
    TEST_ASSERT_FLOAT_WITHIN(MAX_ABS_ERROR, 0.3, output[2]);
    TEST_ASSERT_FLOAT_WITHIN(MAX_ABS_ERROR, 0.4, output[3]);
    TEST_ASSERT_FLOAT_WITHIN(MAX_ABS_ERROR, 0.3, output[4]);
    TEST_ASSERT_FLOAT_WITHIN(MAX_ABS_ERROR, 0.2, output[5]);
    TEST_ASSERT_FLOAT_WITHIN(MAX_ABS_ERROR, 0.1, output[6]);
}

void test_isEnabled_mute()
{
    float input[TEST_BLOCK_SIZE] = {0.1, 0.2, 0.3, 0.4, 0.3, 0.2, 0.1};

    mute.setIsEnabled(false);
    float* output = mute.process(input);

    TEST_ASSERT_FLOAT_WITHIN(MAX_ABS_ERROR, 0.1, output[0]);
    TEST_ASSERT_FLOAT_WITHIN(MAX_ABS_ERROR, 0.2, output[1]);
    TEST_ASSERT_FLOAT_WITHIN(MAX_ABS_ERROR, 0.3, output[2]);
    TEST_ASSERT_FLOAT_WITHIN(MAX_ABS_ERROR, 0.4, output[3]);
    TEST_ASSERT_FLOAT_WITHIN(MAX_ABS_ERROR, 0.3, output[4]);
    TEST_ASSERT_FLOAT_WITHIN(MAX_ABS_ERROR, 0.2, output[5]);
    TEST_ASSERT_FLOAT_WITHIN(MAX_ABS_ERROR, 0.1, output[6]);
}

void setup()
{
    Serial.begin(9600);

    delay(5000);

    Serial.printf("Processing tests:\n");
    RUN_TEST(test_biquad);
    RUN_TEST(test_feedbackComb);
    RUN_TEST(test_allPassComb);

    RUN_TEST(test_contour);
    RUN_TEST(test_presence);
    RUN_TEST(test_eq);
    RUN_TEST(test_compressor);
    RUN_TEST(test_octaver);
    RUN_TEST(test_delay);
    RUN_TEST(test_reverb);
    RUN_TEST(test_overdrive);
    RUN_TEST(test_mute);

    RUN_TEST(test_performance);

    RUN_TEST(test_isEnabled_contour);
    RUN_TEST(test_isEnabled_presence);
    RUN_TEST(test_isEnabled_eq);
    RUN_TEST(test_isEnabled_compressor);
    RUN_TEST(test_isEnabled_octaver);
    RUN_TEST(test_isEnabled_delay);
    RUN_TEST(test_isEnabled_reverb);
    RUN_TEST(test_isEnabled_overdrive);
    RUN_TEST(test_isEnabled_mute);
}

void loop()
{
}

#endif
