mamaheux/bass-amplifier/code/common/test/EffectDesignTests/PresenceDesignerTests.cpp

#include <unity.h>
#include <EffectDesign.h>

#include "PresenceDesignerTests.h"

constexpr float MAX_ABS_ERROR = 0.0001;

static void test_PresenceDesigner_getters()
{
    constexpr float SAMPLING_FREQUENCY = 48000;
    PresenceDesigner designer(SAMPLING_FREQUENCY);

    TEST_ASSERT_EQUAL(SAMPLING_FREQUENCY, designer.samplingFrequency());
    TEST_ASSERT_EQUAL(1, designer.effectCode());
    TEST_ASSERT_EQUAL(24, designer.dataSize());
    TEST_ASSERT_EQUAL(true, designer.isDirty());


    designer.update(0);
    designer.setIsEnabled(false);
    TEST_ASSERT_EQUAL(false, designer.isActive());

    designer.setIsEnabled(true);
    TEST_ASSERT_EQUAL(false, designer.isActive());

    designer.update(1);
    TEST_ASSERT_EQUAL(true, designer.isActive());
}

static void test_PresenceDesigner_update()
{
    constexpr float SAMPLING_FREQUENCY = 48000;
    constexpr uint8_t GAIN = 255;

    PresenceDesigner designer(SAMPLING_FREQUENCY);

    designer.setIsDirty(false);
    designer.update(GAIN);
    TEST_ASSERT_EQUAL(true, designer.isDirty());

    const float* data = reinterpret_cast<const float*>(designer.data());

    // High shelving filter
    TEST_ASSERT_FLOAT_WITHIN(MAX_ABS_ERROR, 1.90986258, data[0]);
    TEST_ASSERT_FLOAT_WITHIN(MAX_ABS_ERROR, -3.40873779, data[1]);
    TEST_ASSERT_FLOAT_WITHIN(MAX_ABS_ERROR, 1.5135854, data[2]);
    TEST_ASSERT_FLOAT_WITHIN(MAX_ABS_ERROR, 1.70474705, data[3]);
    TEST_ASSERT_FLOAT_WITHIN(MAX_ABS_ERROR, -0.71945724, data[4]);

    // Global gain
    TEST_ASSERT_FLOAT_WITHIN(MAX_ABS_ERROR, 0.5012, data[5]);
    

    designer.setIsDirty(false);
    designer.update(GAIN);
    TEST_ASSERT_EQUAL(false, designer.isDirty());
}

void runPresenceDesignerTests()
{
    RUN_TEST(test_PresenceDesigner_getters);
    RUN_TEST(test_PresenceDesigner_update);
}
